bakudr18/RubiksCubeRobot/STL/plate_86duino.STL

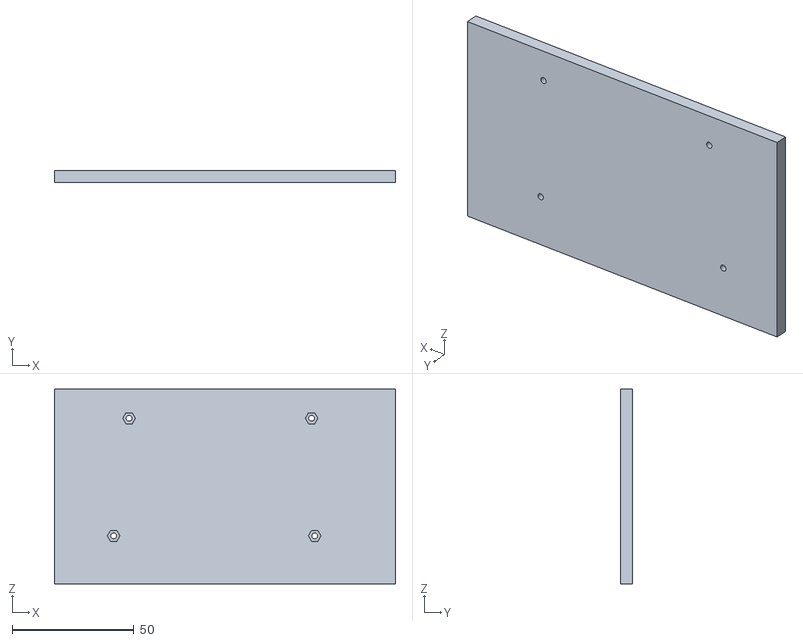
[picture p15: CAD file, 2019-08-08]
STL/plate_86duino.STL
140.0 x 5.00 x 80.0
