bakudr18/RubiksCubeRobot/STL/pillar.STL

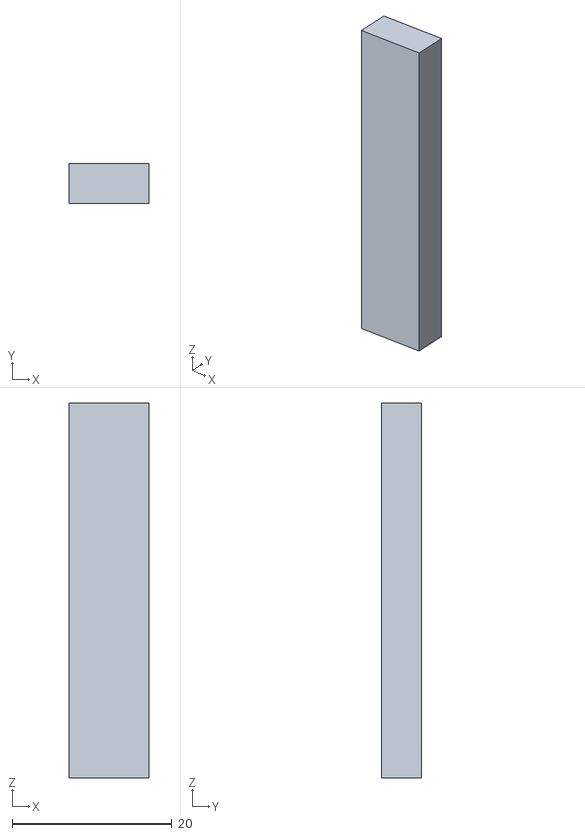
[picture p16: CAD file, 2019-08-08]
STL/pillar.STL
10.0 x 5.00 x 47.0
