bakudr18/RubiksCubeRobot/STL/cover.STL

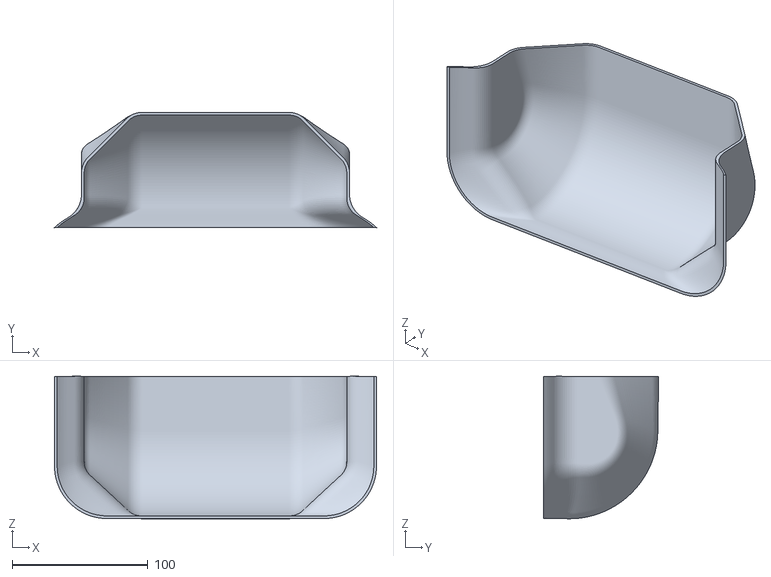
[picture p17: CAD file, 2019-08-08]
STL/cover.STL
237.6 x 85.0 x 105.2
