bakudr18/RubiksCubeRobot/STL/joint2.STL

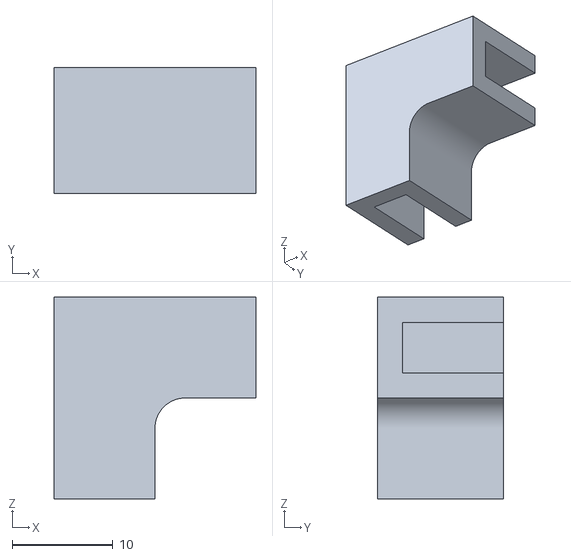
[picture p18: CAD file, 2019-08-08]
STL/joint2.STL
20.0 x 12.5 x 20.0
