bakudr18/RubiksCubeRobot/STL/joint5.STL

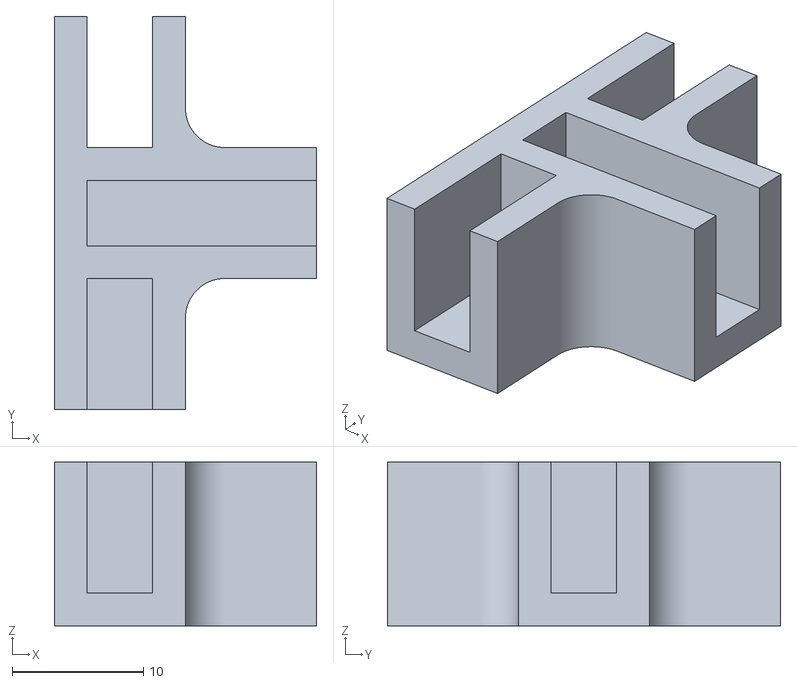
[picture p19: CAD file, 2019-08-08]
STL/joint5.STL
20.0 x 30.0 x 12.5
