bakudr18/RubiksCubeRobot/STL/arm_left.STL

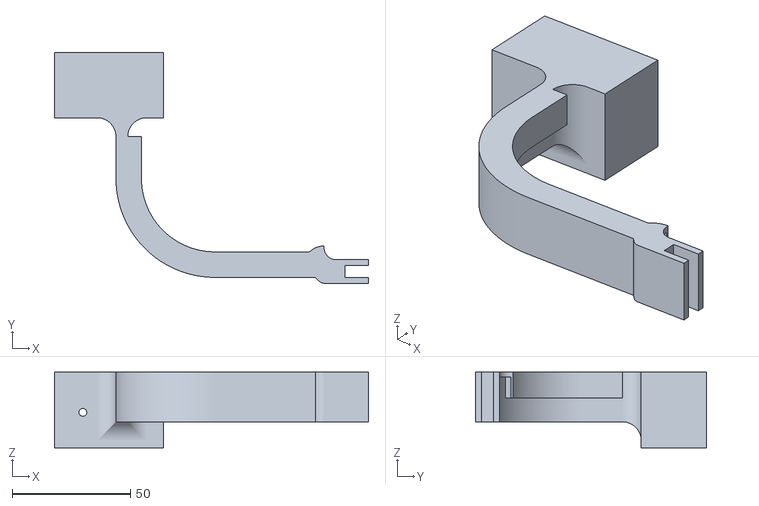
[picture p20: CAD file, 2019-08-08]
STL/arm_left.STL
132.8 x 97.5 x 32.0
