bakudr18/RubiksCubeRobot/STL/pillar_short.STL

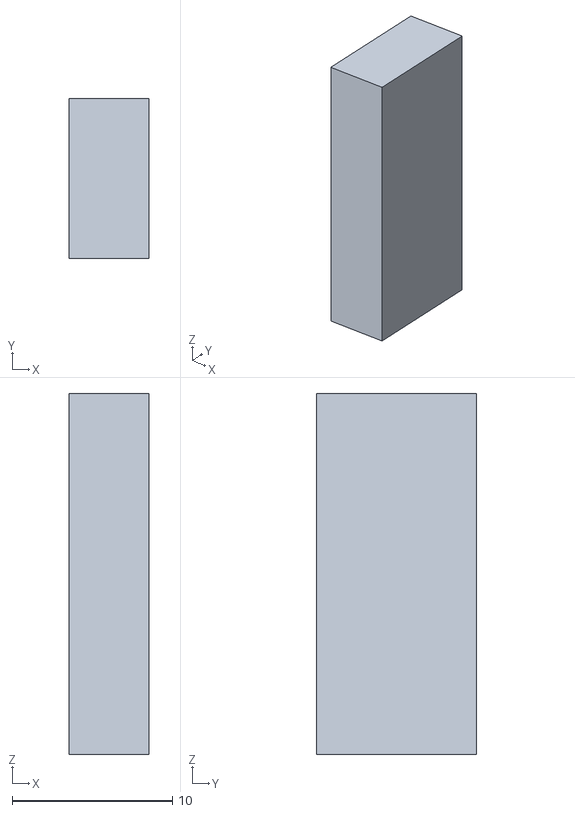
[picture p21: CAD file, 2019-08-08]
STL/pillar_short.STL
5.00 x 10.0 x 22.5
