bakudr18/RubiksCubeRobot/STL/plate_bottom.STL

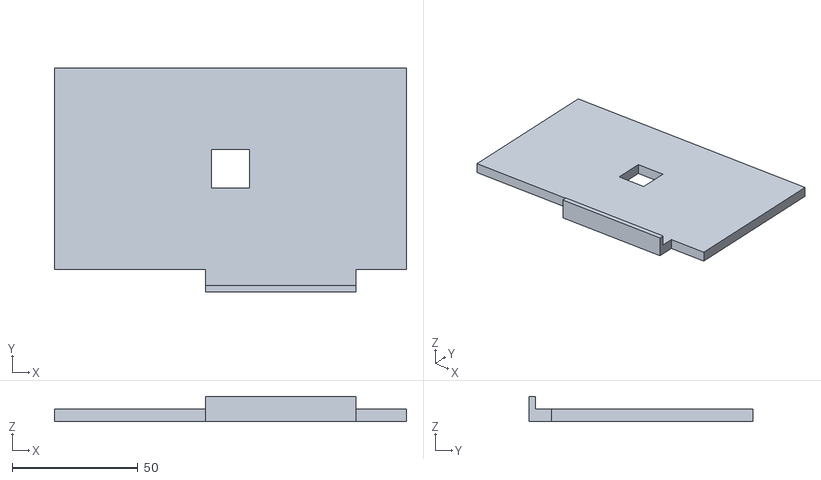
[picture p22: CAD file, 2019-08-08]
STL/plate_bottom.STL
140.0 x 89.0 x 10.0
